Poblit0/Atlas/Rapports séances/DELFLY Agathe/Séance 2/séance2.pdf

Séance 2 :

Objectifs de séance :
- Faire fonctionner les moteurs via le pont en H
- Fixer les composants sur l’étage 0

J’ai soudé les fils sur les moteurs puis j’ai fait fonctionner les moteurs via le pont en H.

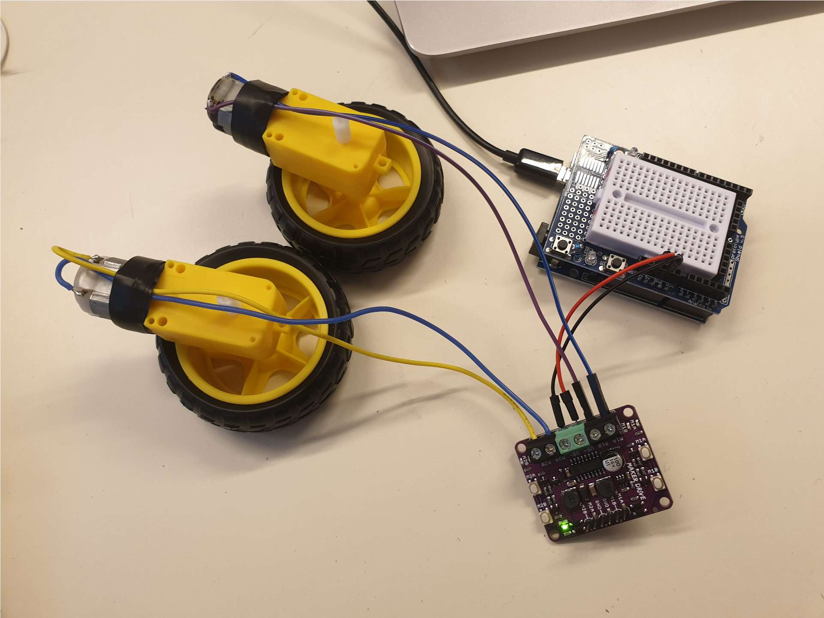
[picture p81: figure]

En utilisant Inkscape et la découpeuse laser, j’ai réalisé des supports en bois qui permettent de fixer les moteurs à l’étage 0.

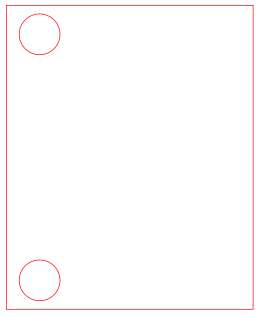
[picture p82: figure]
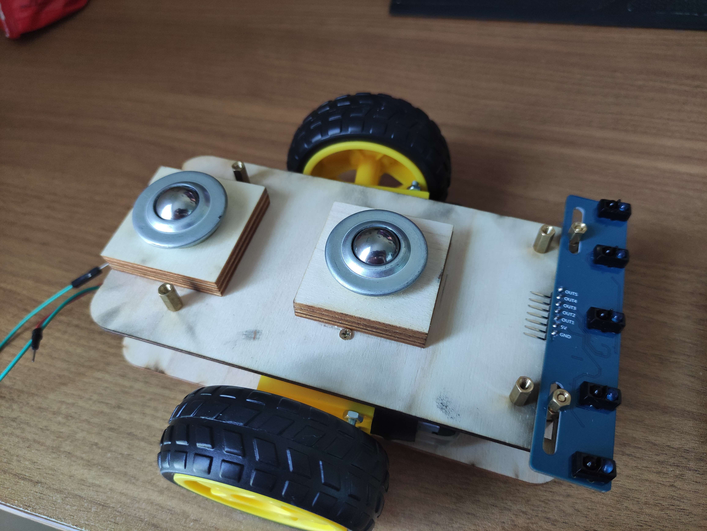
[picture p83: figure]

Objectif de la prochaine séance : Faire le code pour suivre la ligne
