Poblit0/Atlas/Rapports séances/MAUVOISIN Paul/Séance 4/Code Arduino/IR_analog.ino

const int IN_A0 = A0;  // analog input
const int IN_D0 = 7;   // digital input
const int IN_A1 = A1;  // analog input
const int IN_D1 = 8;   // digital input
void setup() {
  Serial.begin(9600);
  pinMode(IN_A0, INPUT);
  pinMode(IN_D0, INPUT);
  pinMode(IN_A1, INPUT);
  pinMode(IN_D1, INPUT);
}

int value_A0;
bool value_D0;
int value_A1;
bool value_D1;

void loop() {
  value_A0 = analogRead(IN_A0);   // reads the analog input from the IR distance sensor
  value_D0 = digitalRead(IN_D0);  // reads the digital input from the IR distance sensor
  value_A1 = analogRead(IN_A1);   // reads the analog input from the IR distance sensor
  value_D1 = digitalRead(IN_D1);  // reads the digital input from the IR distance sensor
  Serial.print(" Analogue = ");
  Serial.println(value_A0);
  //Serial.print(" Analogue = ");
  //Serial.println(value_A1);
  // Serial.print(" Digital =");
  // Serial.print(value_D0);
  // Serial.print(" Digital =");
  // Serial.println(value_D1);
  delay(100);
}
